rrainey/DSKY-digital-indicator-replica/images/render-03.png

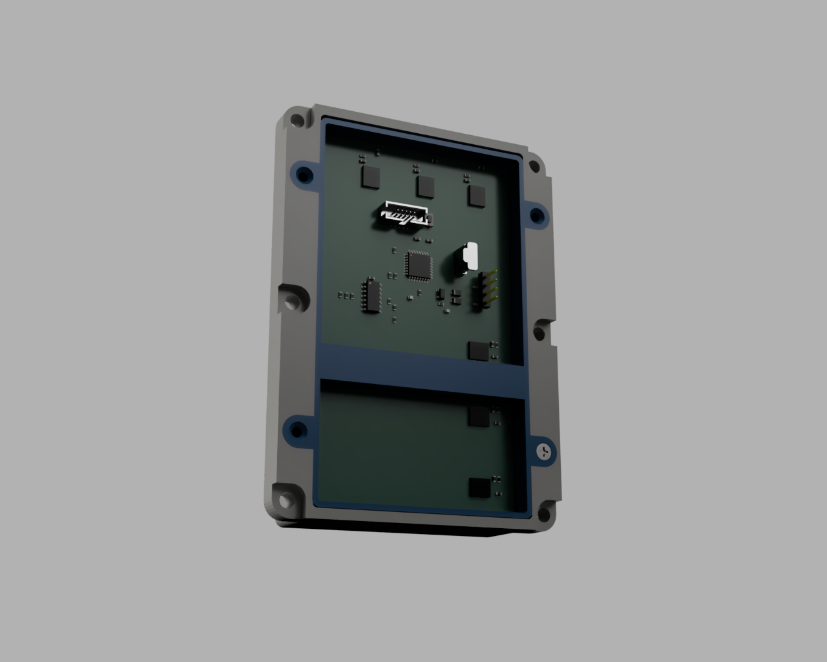
images/render-03.png
