rrainey/DSKY-digital-indicator-replica/images/transparent-pcb.PNG

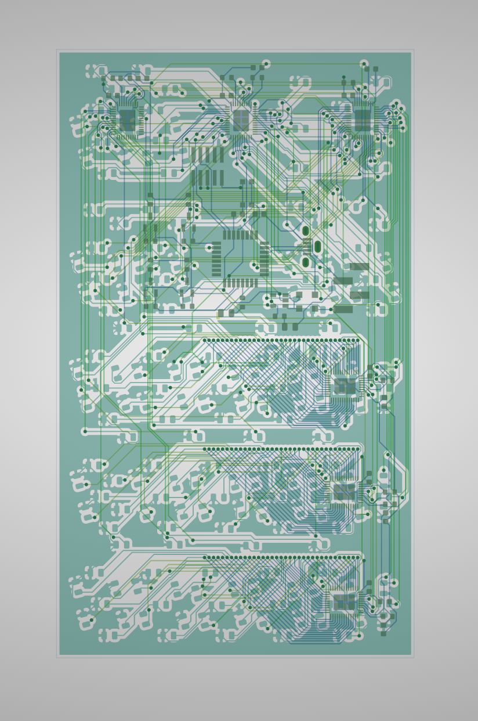
images/transparent-pcb.PNG
